kinematicdigit/MiniRabbitBurner_Dual_Sensor/media/IMG_7574.jpeg

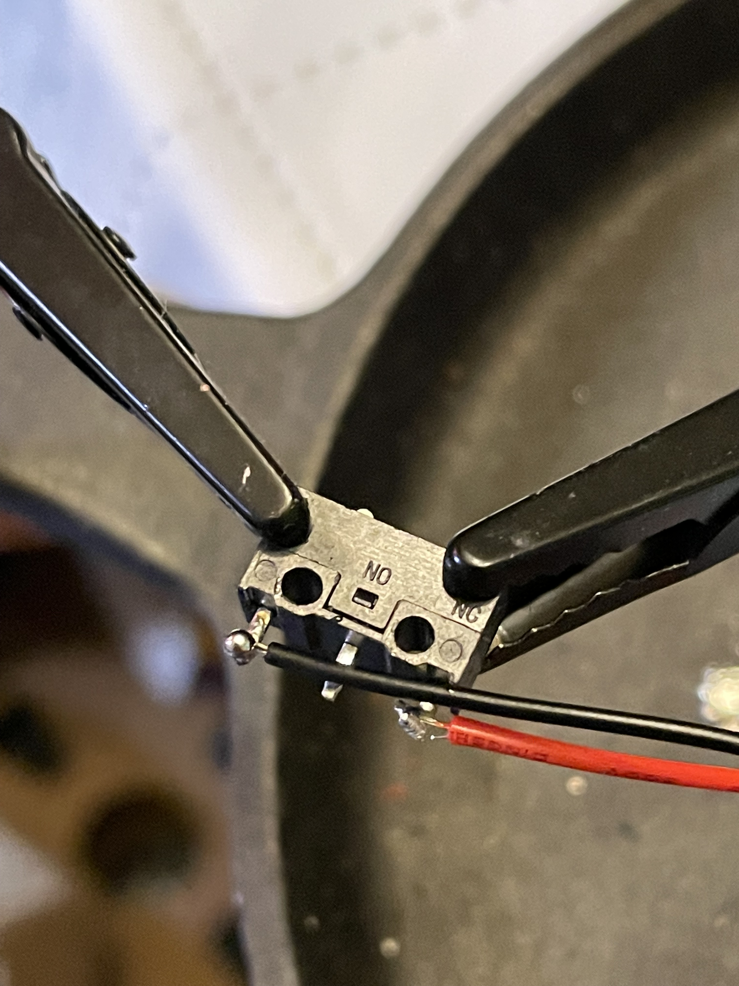
media/IMG_7574.jpeg
