kinematicdigit/MiniRabbitBurner_Dual_Sensor/media/IMG_7576.jpeg

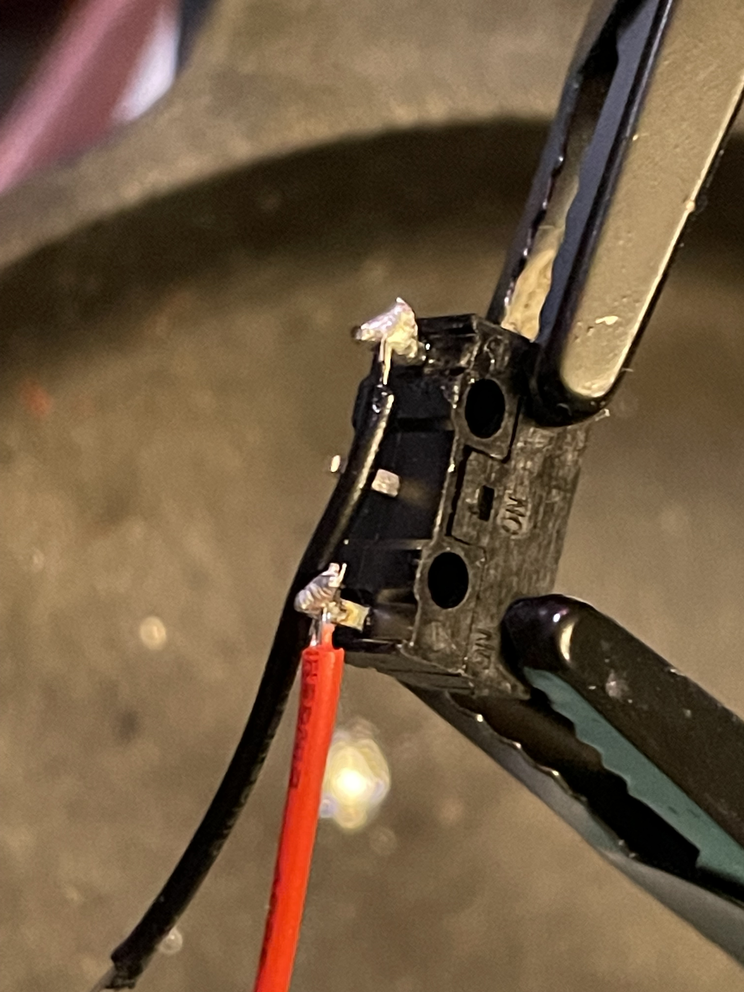
media/IMG_7576.jpeg
