kinematicdigit/MiniRabbitBurner_Dual_Sensor/media/IMG_7577.jpeg

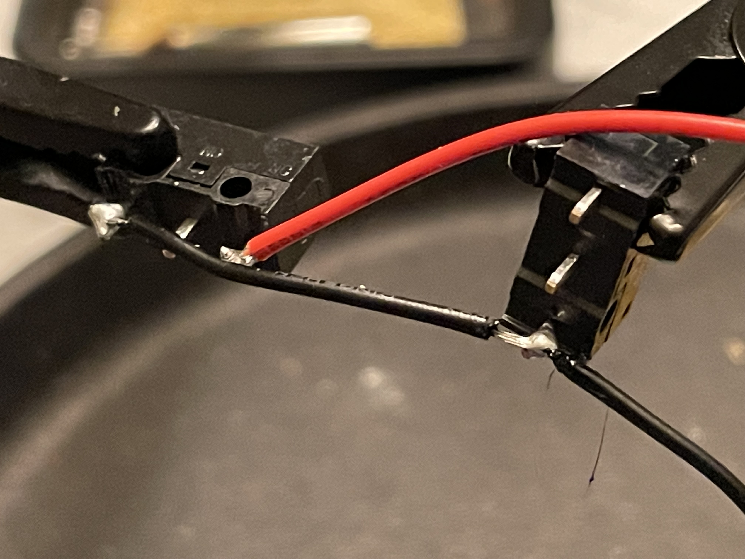
media/IMG_7577.jpeg
