kinematicdigit/MiniRabbitBurner_Dual_Sensor/media/IMG_7578.jpeg

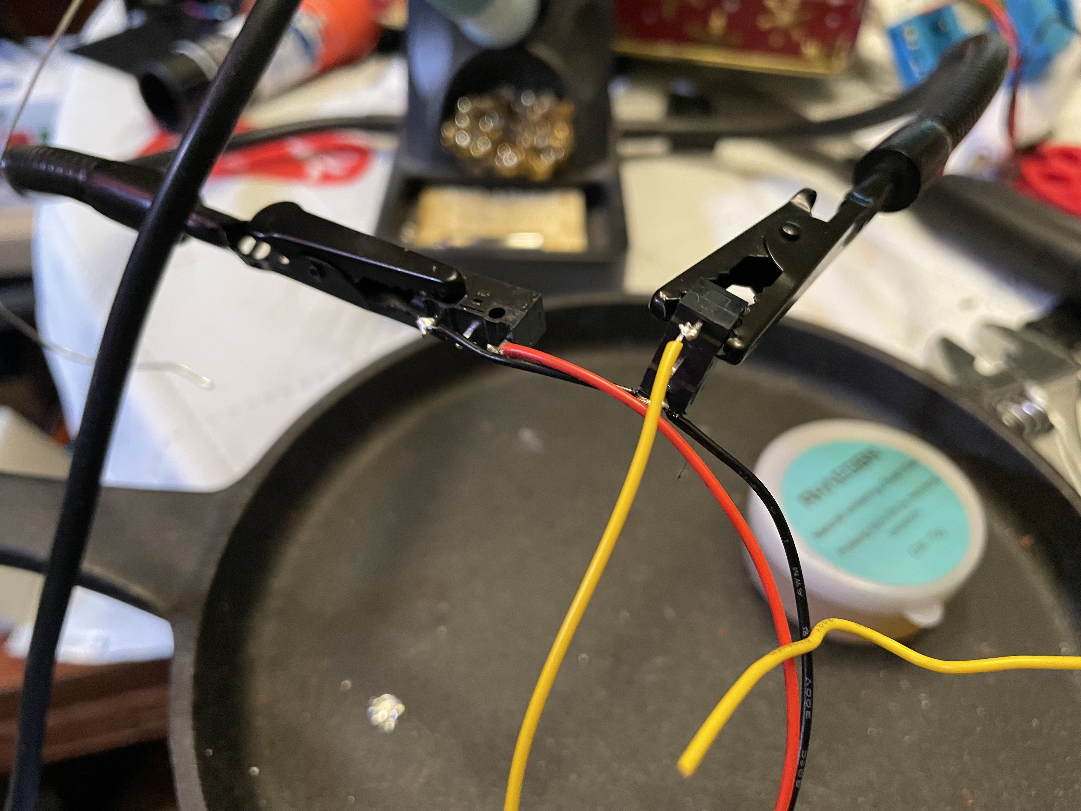
media/IMG_7578.jpeg
