kinematicdigit/MiniRabbitBurner_Dual_Sensor/media/IMG_7579.jpeg

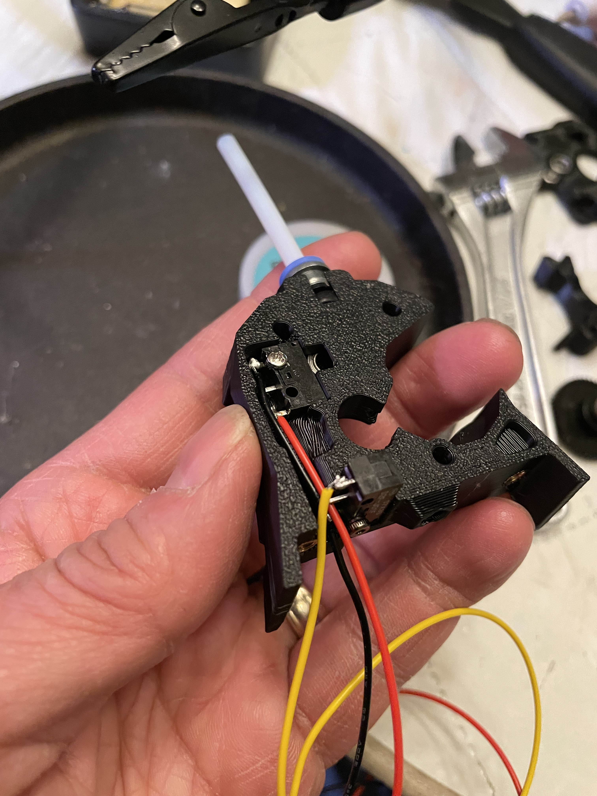
media/IMG_7579.jpeg
